alvarezpuentesjesus-maker/Zanfona-MIDI/Hardware/Piezas_Individuales/Teclas/Inferior_10_Inferior.dxf

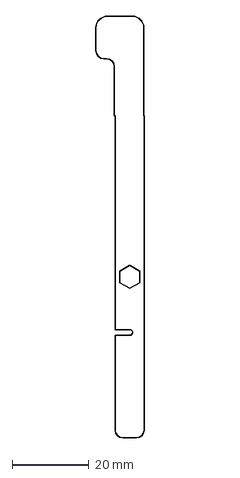
[picture p15: CAD file, 2026-08-17]
Hardware/Piezas_Individuales/Teclas/Inferior_10_Inferior.dxf
12.5 x 110.0 mm
