alvarezpuentesjesus-maker/Zanfona-MIDI/Hardware/Piezas_Individuales/Caja_Teclas/Caja_Tapa_Enganches.dxf

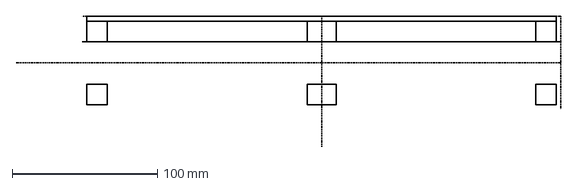
[picture p16: CAD file, 2026-08-17]
Hardware/Piezas_Individuales/Caja_Teclas/Caja_Tapa_Enganches.dxf
375.6 x 89.7 mm
