alvarezpuentesjesus-maker/Zanfona-MIDI/Hardware/Piezas_Individuales/Cuerpo/Cuerpo_Refuerzo2.dxf

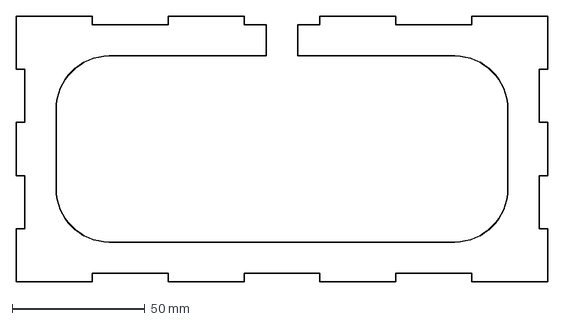
[picture p17: CAD file, 2026-08-17]
Hardware/Piezas_Individuales/Cuerpo/Cuerpo_Refuerzo2.dxf
200.0 x 100.0 mm
