alvarezpuentesjesus-maker/Zanfona-MIDI/Hardware/Piezas_Individuales/Teclas/Inferior_9_Inferior.dxf

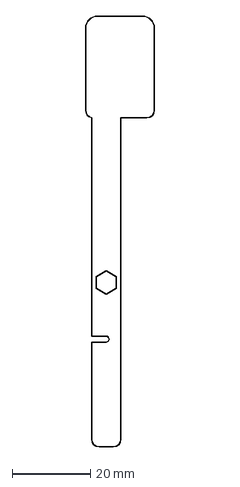
[picture p18: CAD file, 2026-08-17]
Hardware/Piezas_Individuales/Teclas/Inferior_9_Inferior.dxf
17.5 x 110.0 mm
