alvarezpuentesjesus-maker/Zanfona-MIDI/Hardware/Piezas_Individuales/Caja_Teclas/Clavija_Arriba.dxf

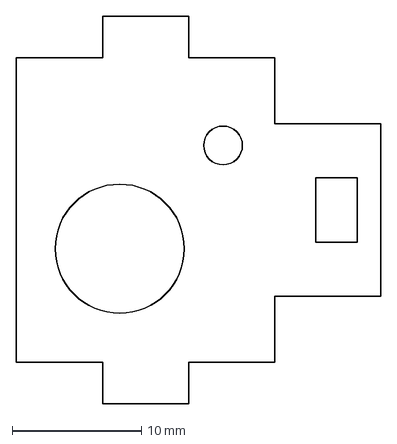
[picture p19: CAD file, 2026-08-17]
Hardware/Piezas_Individuales/Caja_Teclas/Clavija_Arriba.dxf
28.2 x 30.0 mm
