alvarezpuentesjesus-maker/Zanfona-MIDI/Hardware/Piezas_Individuales/Cuerpo/Manivela_Enganche.dxf

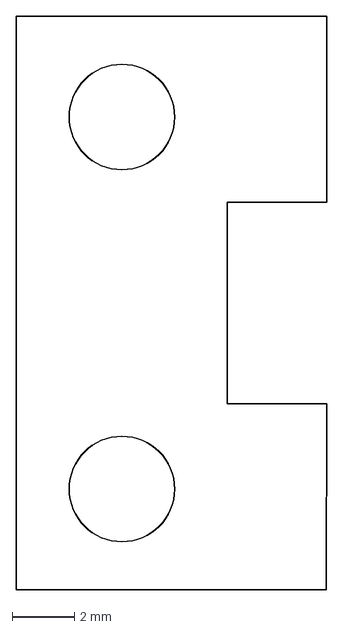
[picture p20: CAD file, 2026-08-17]
Hardware/Piezas_Individuales/Cuerpo/Manivela_Enganche.dxf
10.00 x 18.5 mm
