alvarezpuentesjesus-maker/Zanfona-MIDI/Hardware/Piezas_Individuales/Teclas/Cabeza_10.dxf

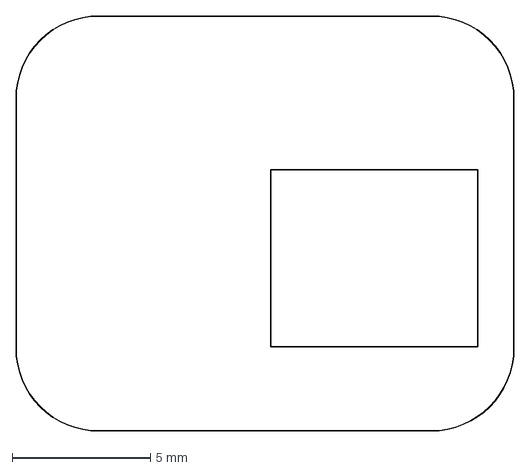
[picture p21: CAD file, 2026-08-17]
Hardware/Piezas_Individuales/Teclas/Cabeza_10.dxf
18.0 x 15.0 mm
