alvarezpuentesjesus-maker/Zanfona-MIDI/Hardware/Piezas_Individuales/Caja_Teclas/Clavija_Perno.dxf

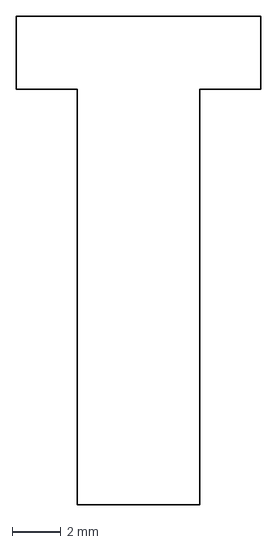
[picture p22: CAD file, 2026-08-17]
Hardware/Piezas_Individuales/Caja_Teclas/Clavija_Perno.dxf
10.00 x 20.0 mm
