alvarezpuentesjesus-maker/Zanfona-MIDI/Hardware/Piezas_Individuales/Cuerpo/Cuerpo_Lateral_Manivela.dxf

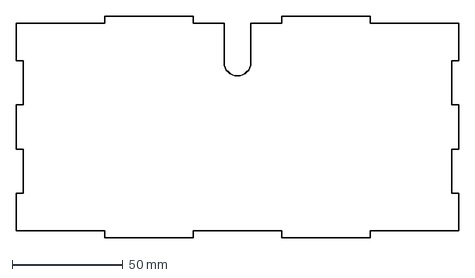
[picture p23: CAD file, 2026-08-17]
Hardware/Piezas_Individuales/Cuerpo/Cuerpo_Lateral_Manivela.dxf
200.0 x 100.0 mm
