alvarezpuentesjesus-maker/Zanfona-MIDI/Hardware/Piezas_Individuales/Caja_Teclas/Caja_Lateral_Largo2.dxf

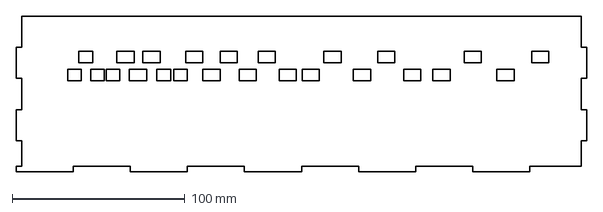
[picture p25: CAD file, 2026-08-17]
Hardware/Piezas_Individuales/Caja_Teclas/Caja_Lateral_Largo2.dxf
330.0 x 90.0 mm
