alvarezpuentesjesus-maker/Zanfona-MIDI/Hardware/Piezas_Individuales/Cuerpo/Cuerpo_Lateral_Corto.dxf

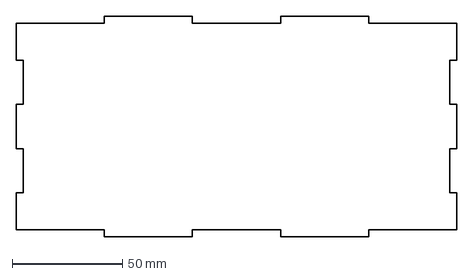
[picture p26: CAD file, 2026-08-17]
Hardware/Piezas_Individuales/Cuerpo/Cuerpo_Lateral_Corto.dxf
200.0 x 100.0 mm
