alvarezpuentesjesus-maker/Zanfona-MIDI/Hardware/Piezas_Individuales/Teclas/Inferior_2_Superior.dxf

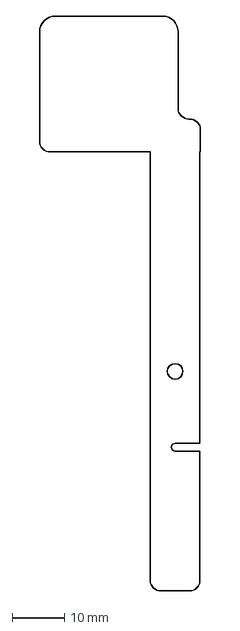
[picture p27: CAD file, 2026-08-17]
Hardware/Piezas_Individuales/Teclas/Inferior_2_Superior.dxf
30.8 x 110.0 mm
