alvarezpuentesjesus-maker/Zanfona-MIDI/Hardware/Piezas_Individuales/Caja_Teclas/Caja_Lateral_Largo1.dxf

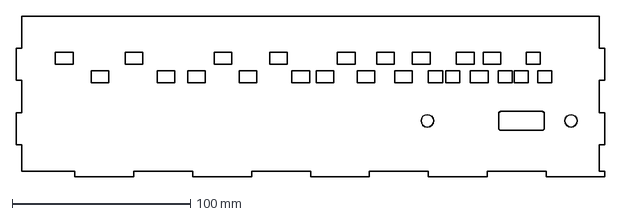
[picture p28: CAD file, 2026-08-17]
Hardware/Piezas_Individuales/Caja_Teclas/Caja_Lateral_Largo1.dxf
330.0 x 90.0 mm
