alvarezpuentesjesus-maker/Zanfona-MIDI/Hardware/Piezas_Individuales/Cuerpo/Sopoerte_Rueda_Superior_Tapa.dxf

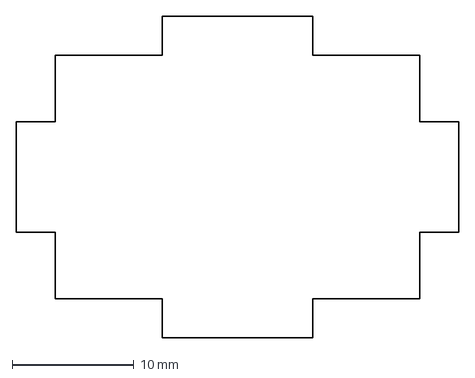
[picture p29: CAD file, 2026-08-17]
Hardware/Piezas_Individuales/Cuerpo/Sopoerte_Rueda_Superior_Tapa.dxf
36.4 x 26.4 mm
