alvarezpuentesjesus-maker/Zanfona-MIDI/Hardware/Piezas_Individuales/Caja_Teclas/Caja_Base.dxf

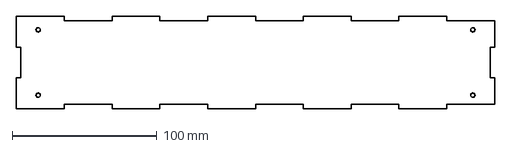
[picture p31: CAD file, 2026-08-17]
Hardware/Piezas_Individuales/Caja_Teclas/Caja_Base.dxf
330.0 x 64.0 mm
