alvarezpuentesjesus-maker/Zanfona-MIDI/Hardware/Piezas_Individuales/Cuerpo/Cuerpo_Tapa.dxf

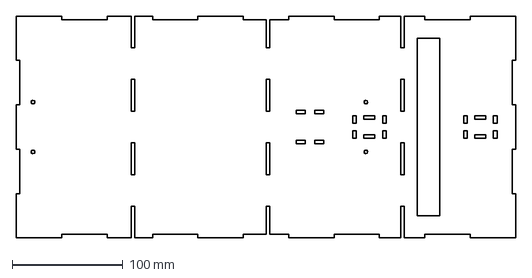
[picture p32: CAD file, 2026-08-17]
Hardware/Piezas_Individuales/Cuerpo/Cuerpo_Tapa.dxf
450.0 x 200.0 mm
