alvarezpuentesjesus-maker/Zanfona-MIDI/Hardware/Piezas_Individuales/Teclas/Inferior_4_Inferior.dxf

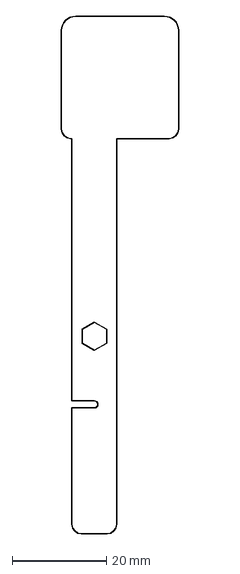
[picture p33: CAD file, 2026-08-17]
Hardware/Piezas_Individuales/Teclas/Inferior_4_Inferior.dxf
24.9 x 110.0 mm
