alvarezpuentesjesus-maker/Zanfona-MIDI/Hardware/Piezas_Individuales/Caja_Teclas/Caja_Soporte_Teclas.dxf

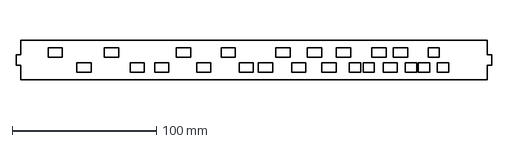
[picture p34: CAD file, 2026-08-17]
Hardware/Piezas_Individuales/Caja_Teclas/Caja_Soporte_Teclas.dxf
330.0 x 27.2 mm
