alvarezpuentesjesus-maker/Zanfona-MIDI/Hardware/Piezas_Individuales/Cuerpo/Cuerpo_Lateral_Largo1.dxf

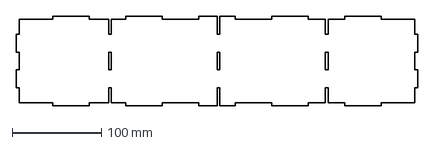
[picture p35: CAD file, 2026-08-17]
Hardware/Piezas_Individuales/Cuerpo/Cuerpo_Lateral_Largo1.dxf
450.0 x 100.0 mm
