alvarezpuentesjesus-maker/Zanfona-MIDI/Hardware/Piezas_Individuales/Teclas/Cabeza_9.dxf

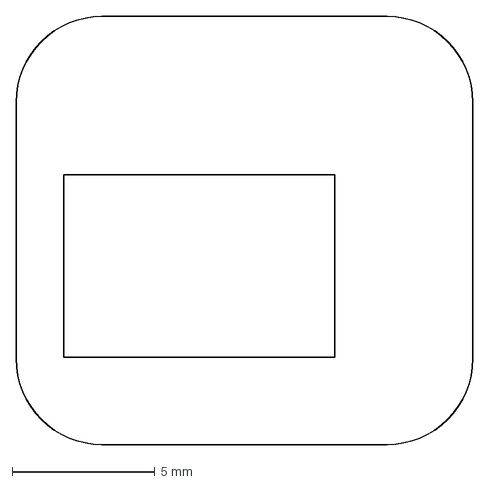
[picture p36: CAD file, 2026-08-17]
Hardware/Piezas_Individuales/Teclas/Cabeza_9.dxf
16.0 x 15.0 mm
