alvarezpuentesjesus-maker/Zanfona-MIDI/Hardware/Piezas_Individuales/Caja_Teclas/Caja_Lateral_Galga.dxf

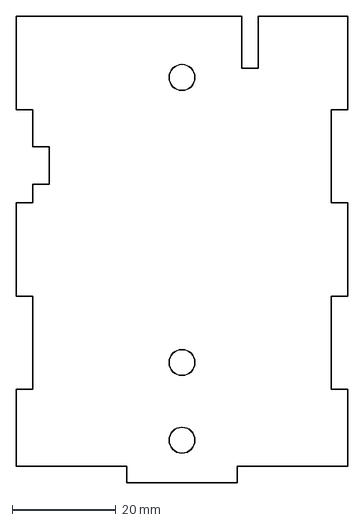
[picture p37: CAD file, 2026-08-17]
Hardware/Piezas_Individuales/Caja_Teclas/Caja_Lateral_Galga.dxf
64.0 x 90.0 mm
