alvarezpuentesjesus-maker/Zanfona-MIDI/Hardware/Piezas_Individuales/Teclas/Inferior_12_Inferior.dxf

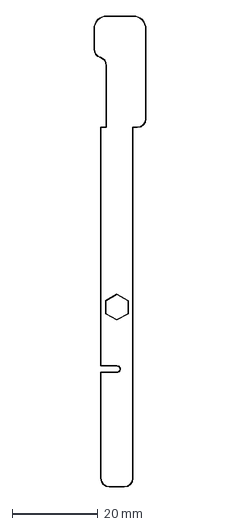
[picture p39: CAD file, 2026-08-17]
Hardware/Piezas_Individuales/Teclas/Inferior_12_Inferior.dxf
12.1 x 110.0 mm
