alvarezpuentesjesus-maker/Zanfona-MIDI/Hardware/Piezas_Individuales/Cuerpo/Soporte_Rueda_Inferior_Laterial.dxf

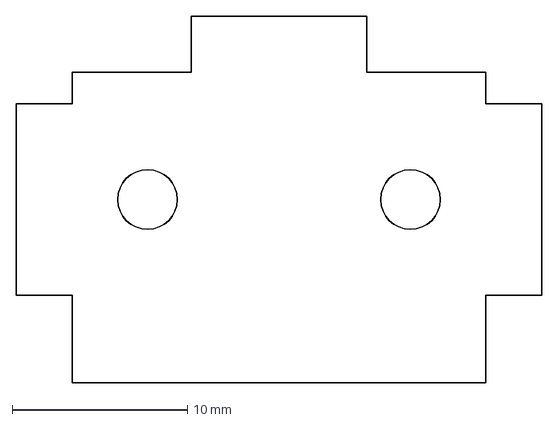
[picture p40: CAD file, 2026-08-17]
Hardware/Piezas_Individuales/Cuerpo/Soporte_Rueda_Inferior_Laterial.dxf
30.0 x 20.9 mm
