alvarezpuentesjesus-maker/Zanfona-MIDI/Hardware/Piezas_Individuales/Teclas/Cabeza_8.dxf

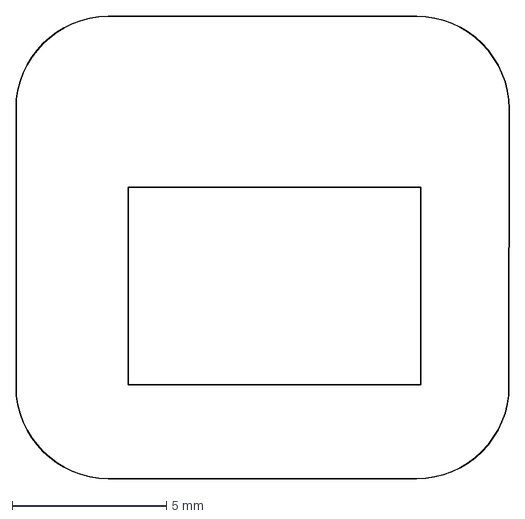
[picture p41: CAD file, 2026-08-17]
Hardware/Piezas_Individuales/Teclas/Cabeza_8.dxf
16.0 x 15.0 mm
