alvarezpuentesjesus-maker/Zanfona-MIDI/Hardware/Piezas_Individuales/Cuerpo/Soporte_Rueda_Inferior_Frente.dxf

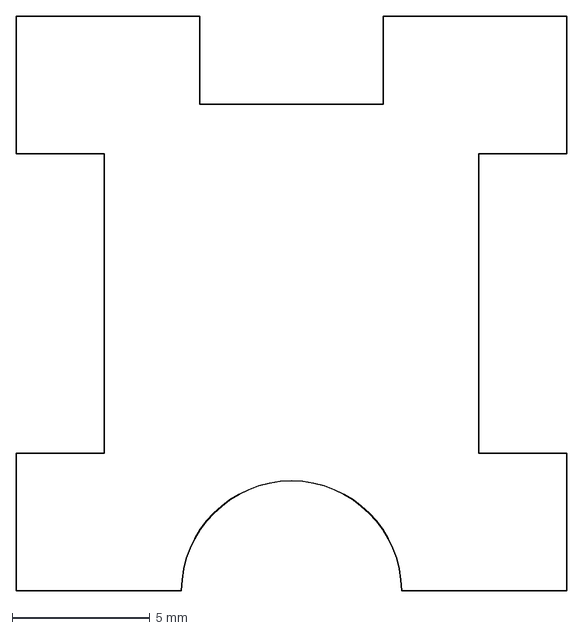
[picture p42: CAD file, 2026-08-17]
Hardware/Piezas_Individuales/Cuerpo/Soporte_Rueda_Inferior_Frente.dxf
20.0 x 20.9 mm
