alvarezpuentesjesus-maker/Zanfona-MIDI/Hardware/Piezas_Individuales/Teclas/Inferior_7_Inferior.dxf

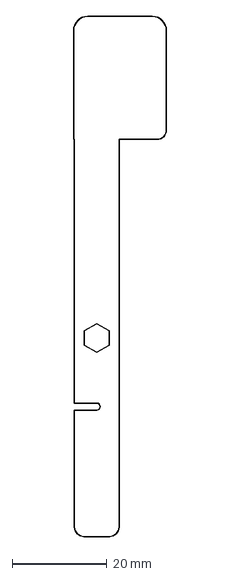
[picture p43: CAD file, 2026-08-17]
Hardware/Piezas_Individuales/Teclas/Inferior_7_Inferior.dxf
19.6 x 110.0 mm
