alvarezpuentesjesus-maker/Zanfona-MIDI/Hardware/Piezas_Individuales/Cuerpo/Cuerpo_Lateral_Largo2.dxf

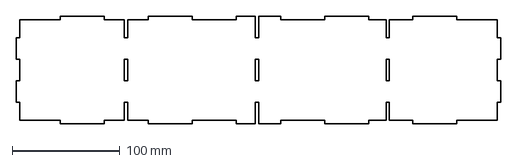
[picture p44: CAD file, 2026-08-17]
Hardware/Piezas_Individuales/Cuerpo/Cuerpo_Lateral_Largo2.dxf
450.0 x 100.0 mm
