alvarezpuentesjesus-maker/Zanfona-MIDI/Hardware/Piezas_Individuales/Teclas/Vástago_Grueso_Inferior.dxf

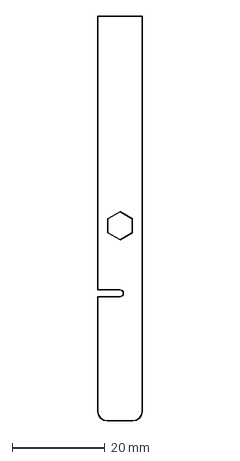
[picture p45: CAD file, 2026-08-17]
Hardware/Piezas_Individuales/Teclas/Vástago_Grueso_Inferior.dxf
9.50 x 87.2 mm
