alvarezpuentesjesus-maker/Zanfona-MIDI/Hardware/Piezas_Individuales/Cuerpo/SopoerteRuerda_Superior_Frente.dxf

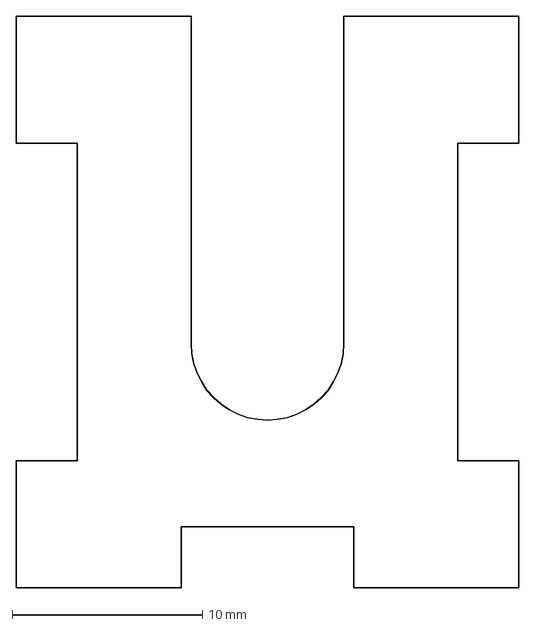
[picture p46: CAD file, 2026-08-17]
Hardware/Piezas_Individuales/Cuerpo/SopoerteRuerda_Superior_Frente.dxf
26.4 x 30.0 mm
