alvarezpuentesjesus-maker/Zanfona-MIDI/Hardware/Piezas_Individuales/Teclas/Inferior_9_Superior.dxf

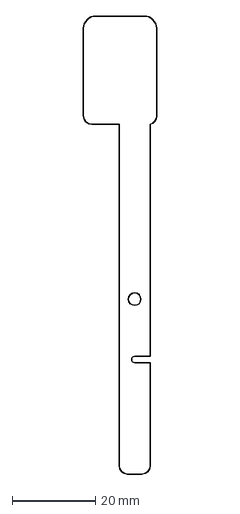
[picture p47: CAD file, 2026-08-17]
Hardware/Piezas_Individuales/Teclas/Inferior_9_Superior.dxf
17.5 x 110.0 mm
