alvarezpuentesjesus-maker/Zanfona-MIDI/Hardware/Piezas_Individuales/Cuerpo/Encoder_Lateral.dxf

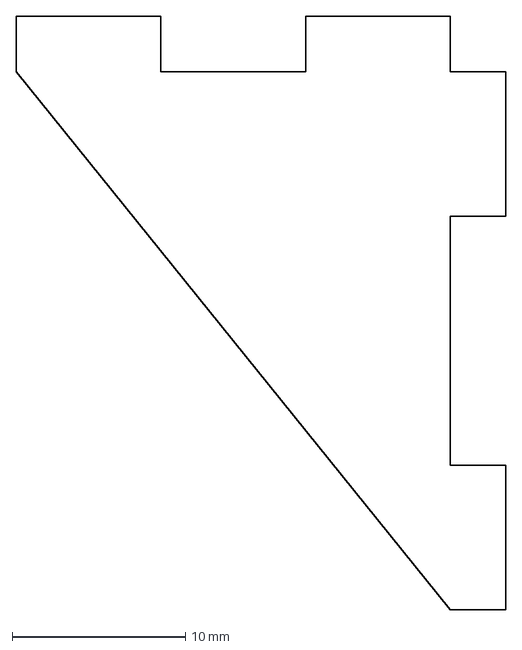
[picture p48: CAD file, 2026-08-17]
Hardware/Piezas_Individuales/Cuerpo/Encoder_Lateral.dxf
28.2 x 34.2 mm
