alvarezpuentesjesus-maker/Zanfona-MIDI/Hardware/Piezas_Individuales/Teclas/Cabeza_1.dxf

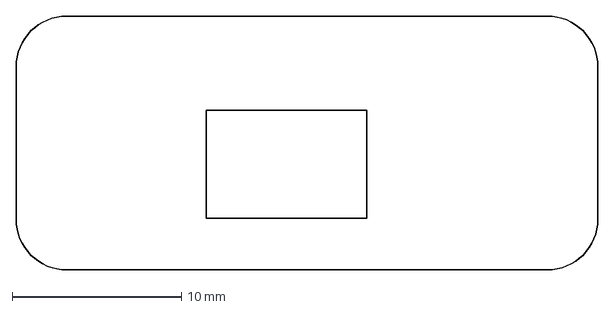
[picture p49: CAD file, 2026-08-17]
Hardware/Piezas_Individuales/Teclas/Cabeza_1.dxf
34.4 x 15.0 mm
