alvarezpuentesjesus-maker/Zanfona-MIDI/Hardware/Piezas_Individuales/Teclas/Cabeza_5.dxf

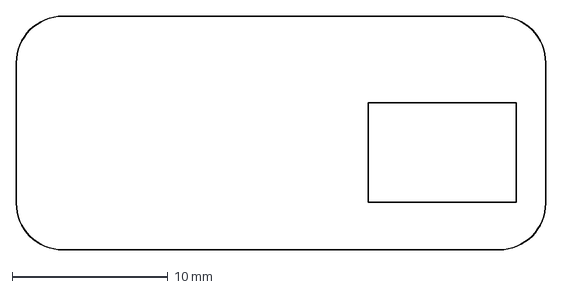
[picture p52: CAD file, 2026-08-17]
Hardware/Piezas_Individuales/Teclas/Cabeza_5.dxf
34.0 x 15.0 mm
