alvarezpuentesjesus-maker/Zanfona-MIDI/Hardware/Piezas_Individuales/Teclas/Vástago_Fino_Superior.dxf

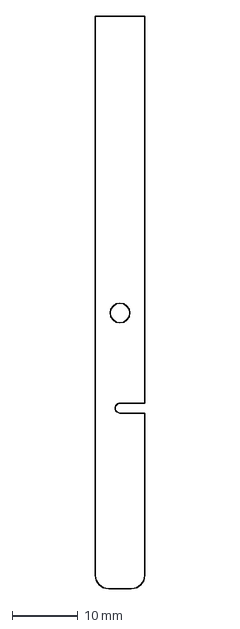
[picture p53: CAD file, 2026-08-17]
Hardware/Piezas_Individuales/Teclas/Vástago_Fino_Superior.dxf
7.50 x 87.2 mm
