alvarezpuentesjesus-maker/Zanfona-MIDI/Hardware/Piezas_Individuales/Teclas/Inferior_13_Inferior.dxf

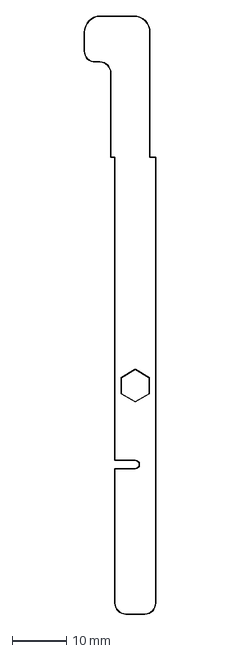
[picture p54: CAD file, 2026-08-17]
Hardware/Piezas_Individuales/Teclas/Inferior_13_Inferior.dxf
13.1 x 110.0 mm
