alvarezpuentesjesus-maker/Zanfona-MIDI/Hardware/Piezas_Individuales/Teclas/Inferior_11_Superior.dxf

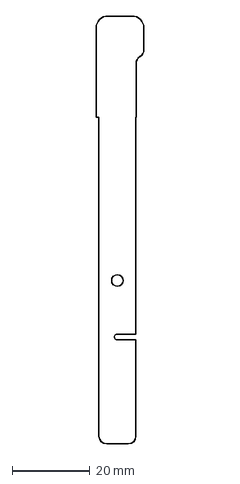
[picture p55: CAD file, 2026-08-17]
Hardware/Piezas_Individuales/Teclas/Inferior_11_Superior.dxf
12.3 x 110.0 mm
