alvarezpuentesjesus-maker/Zanfona-MIDI/Hardware/Piezas_Individuales/Teclas/Cabeza_6.dxf

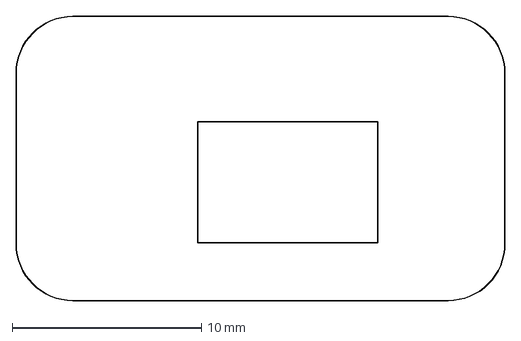
[picture p56: CAD file, 2026-08-17]
Hardware/Piezas_Individuales/Teclas/Cabeza_6.dxf
25.8 x 15.0 mm
