alvarezpuentesjesus-maker/Zanfona-MIDI/Hardware/Piezas_Individuales/Teclas/Inferior_5_Superior.dxf

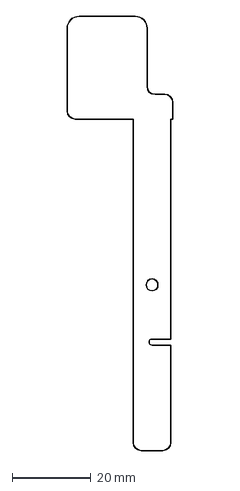
[picture p57: CAD file, 2026-08-17]
Hardware/Piezas_Individuales/Teclas/Inferior_5_Superior.dxf
26.7 x 110.0 mm
