alvarezpuentesjesus-maker/Zanfona-MIDI/Hardware/Piezas_Individuales/Teclas/Cabeza_7.dxf

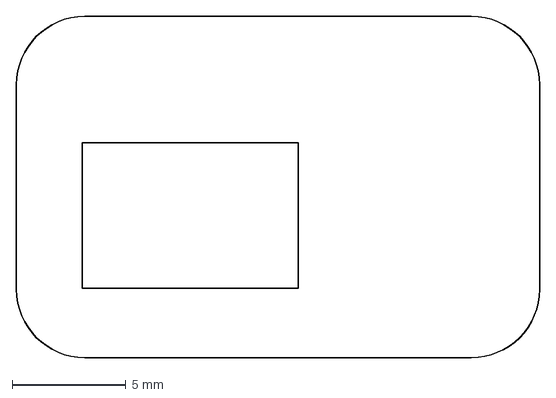
[picture p58: CAD file, 2026-08-17]
Hardware/Piezas_Individuales/Teclas/Cabeza_7.dxf
23.0 x 15.0 mm
