alvarezpuentesjesus-maker/Zanfona-MIDI/Hardware/Piezas_Individuales/Teclas/Inferior_3_Superior.dxf

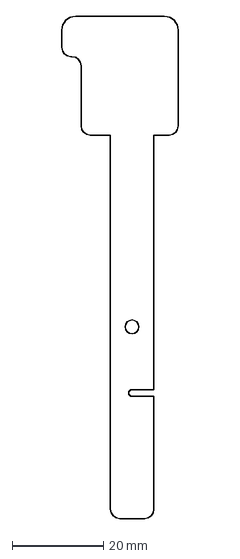
[picture p62: CAD file, 2026-08-17]
Hardware/Piezas_Individuales/Teclas/Inferior_3_Superior.dxf
25.5 x 110.0 mm
