alvarezpuentesjesus-maker/Zanfona-MIDI/Hardware/Piezas_Individuales/Teclas/Vástago_Grueso_Superior.dxf

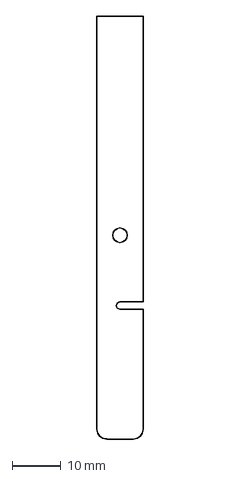
[picture p63: CAD file, 2026-08-17]
Hardware/Piezas_Individuales/Teclas/Vástago_Grueso_Superior.dxf
9.50 x 87.2 mm
