alvarezpuentesjesus-maker/Zanfona-MIDI/Hardware/Piezas_Individuales/Teclas/Inferior_1_Superior.dxf

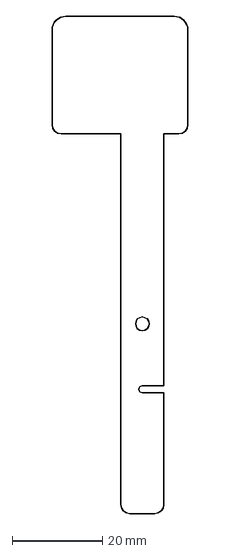
[picture p64: CAD file, 2026-08-17]
Hardware/Piezas_Individuales/Teclas/Inferior_1_Superior.dxf
30.0 x 110.0 mm
