alvarezpuentesjesus-maker/Zanfona-MIDI/Hardware/Piezas_Individuales/Teclas/Inferior_8_Inferior.dxf

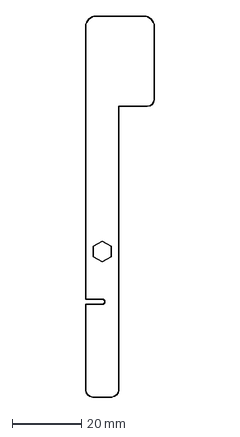
[picture p65: CAD file, 2026-08-17]
Hardware/Piezas_Individuales/Teclas/Inferior_8_Inferior.dxf
19.8 x 110.0 mm
