alvarezpuentesjesus-maker/Zanfona-MIDI/Hardware/Piezas_Individuales/Teclas/Inferior_10_Superior.dxf

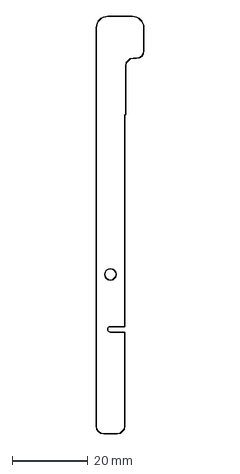
[picture p66: CAD file, 2026-08-17]
Hardware/Piezas_Individuales/Teclas/Inferior_10_Superior.dxf
12.5 x 110.0 mm
