alvarezpuentesjesus-maker/Zanfona-MIDI/Hardware/Piezas_Individuales/Teclas/Cabeza_2.dxf

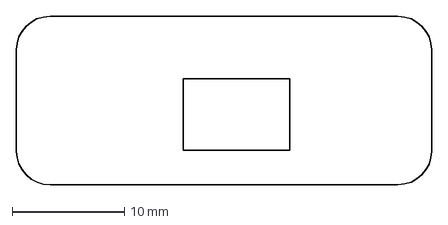
[picture p67: CAD file, 2026-08-17]
Hardware/Piezas_Individuales/Teclas/Cabeza_2.dxf
37.0 x 15.0 mm
