alvarezpuentesjesus-maker/Zanfona-MIDI/Hardware/Piezas_Individuales/Teclas/Cabeza_3.dxf

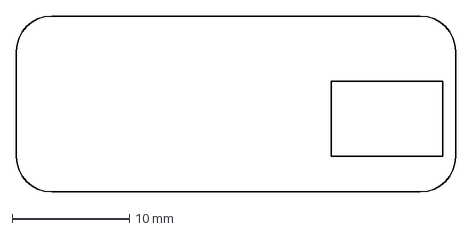
[picture p68: CAD file, 2026-08-17]
Hardware/Piezas_Individuales/Teclas/Cabeza_3.dxf
37.5 x 15.0 mm
