alvarezpuentesjesus-maker/Zanfona-MIDI/Hardware/Piezas_Individuales/Teclas/Inferior_6_Inferior.dxf

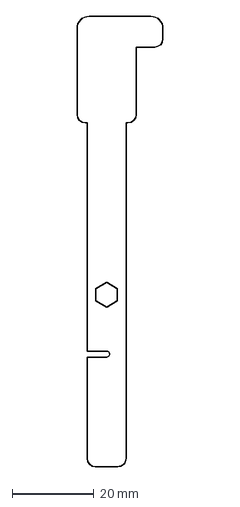
[picture p69: CAD file, 2026-08-17]
Hardware/Piezas_Individuales/Teclas/Inferior_6_Inferior.dxf
21.0 x 110.0 mm
