alvarezpuentesjesus-maker/Zanfona-MIDI/Hardware/Piezas_Individuales/Teclas/Vástago_Fino_Inferior.dxf

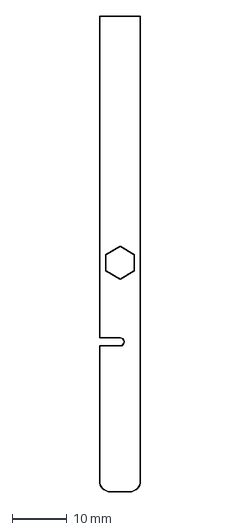
[picture p70: CAD file, 2026-08-17]
Hardware/Piezas_Individuales/Teclas/Vástago_Fino_Inferior.dxf
7.50 x 87.2 mm
