alvarezpuentesjesus-maker/Zanfona-MIDI/Hardware/Piezas_Individuales/Teclas/Cabeza_4.dxf

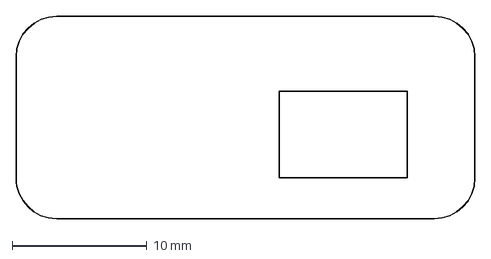
[picture p72: CAD file, 2026-08-17]
Hardware/Piezas_Individuales/Teclas/Cabeza_4.dxf
34.0 x 15.0 mm
