alvarezpuentesjesus-maker/Zanfona-MIDI/Hardware/Piezas_Individuales/Teclas/Inferior_14_Inferior.dxf

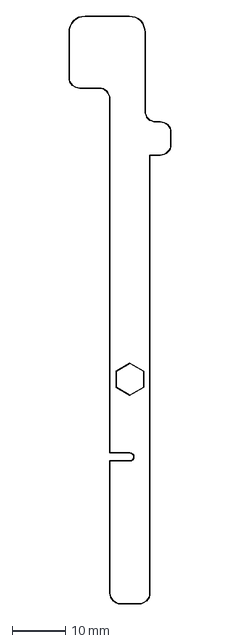
[picture p73: CAD file, 2026-08-17]
Hardware/Piezas_Individuales/Teclas/Inferior_14_Inferior.dxf
19.1 x 110.0 mm
